sadekbaroudi/vulpes-minora/case/mx/vmin-mx-cirque-bottom-left.stl

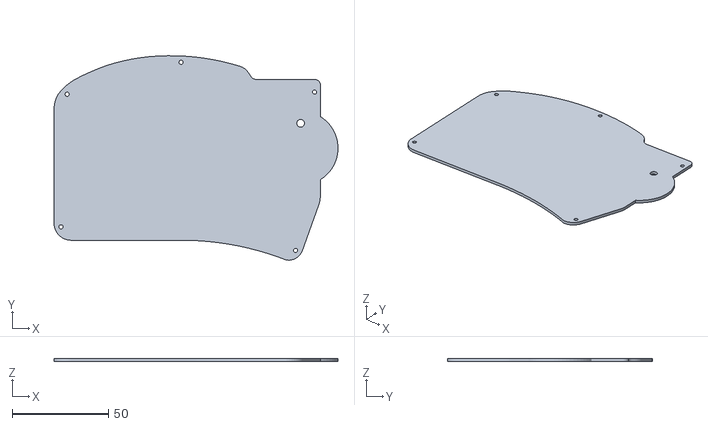
[picture p21: CAD file, 2024-04-24]
case/mx/vmin-mx-cirque-bottom-left.stl
147.2 x 106.0 x 1.60
