sadekbaroudi/vulpes-minora/case/mx/vmin-mx-wireless-cirque-bottom-right.stl

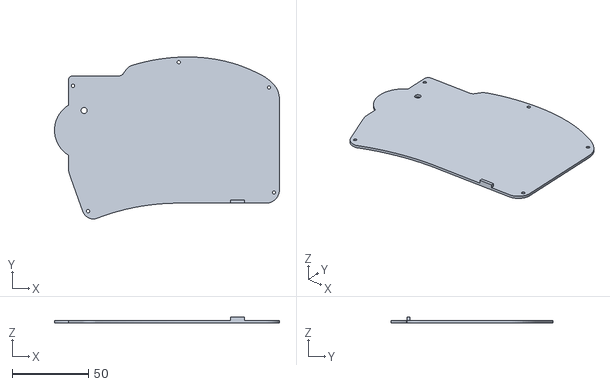
[picture p22: CAD file, 2024-04-24]
case/mx/vmin-mx-wireless-cirque-bottom-right.stl
147.2 x 106.0 x 3.60
