sadekbaroudi/vulpes-minora/case/mx/vmin-vik-peacock-cover.stl

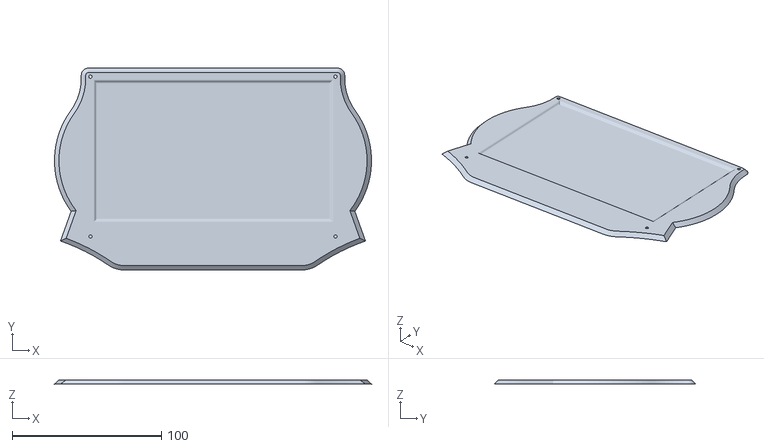
[picture p23: CAD file, 2024-02-21]
case/mx/vmin-vik-peacock-cover.stl
212.2 x 135.2 x 3.00
