sadekbaroudi/vulpes-minora/case/mx/vmin-mx-vik-peacock.stl

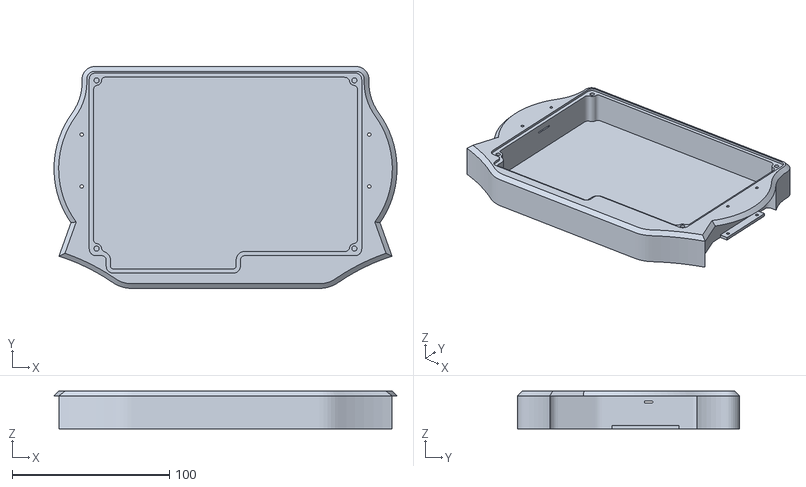
[picture p24: CAD file, 2024-02-19]
case/mx/vmin-mx-vik-peacock.stl
218.2 x 141.2 x 24.0
