sadekbaroudi/vulpes-minora/case/mx/vmin-xivik-mx-vik-waveshare-left.stl

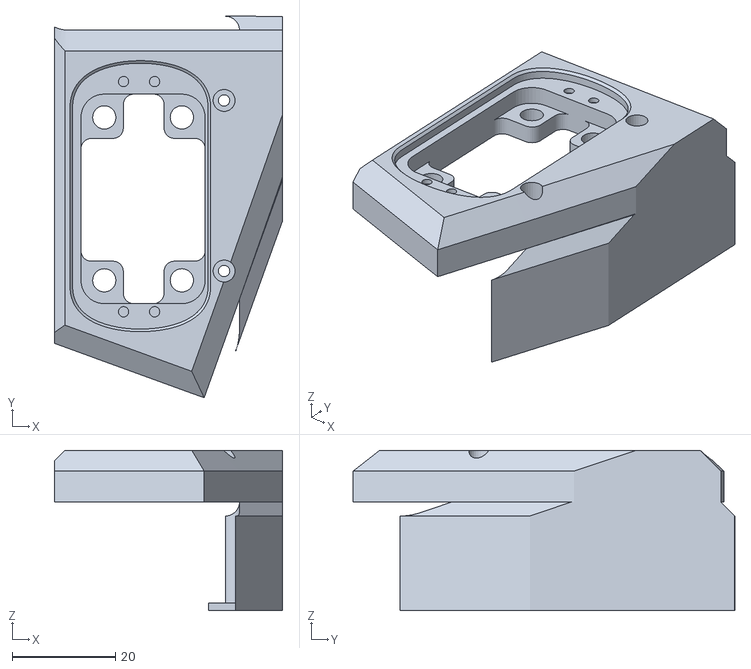
[picture p25: CAD file, 2023-12-03]
case/mx/vmin-xivik-mx-vik-waveshare-left.stl
44.1 x 73.8 x 31.0
