sadekbaroudi/vulpes-minora/case/mx/vmin-xivik-mx-body-left.stl

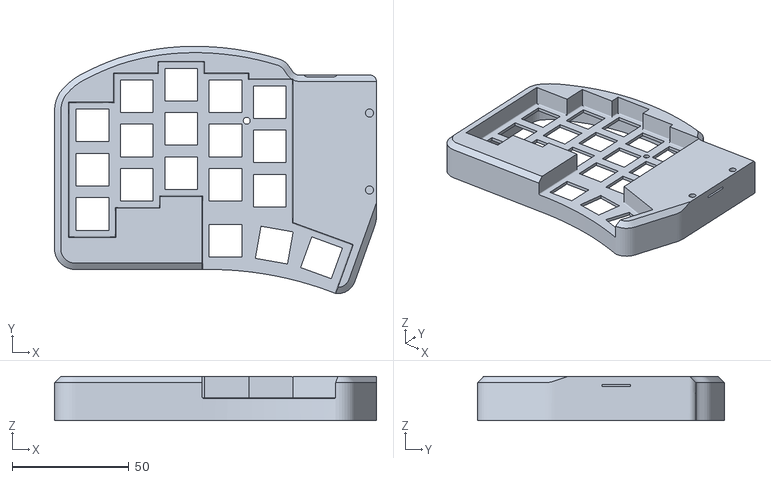
[picture p26: CAD file, 2023-12-01]
case/mx/vmin-xivik-mx-body-left.stl
138.1 x 106.0 x 19.0
