sadekbaroudi/vulpes-minora/case/mx/vmin-pers-cirque-mount-1mm-taller.stl

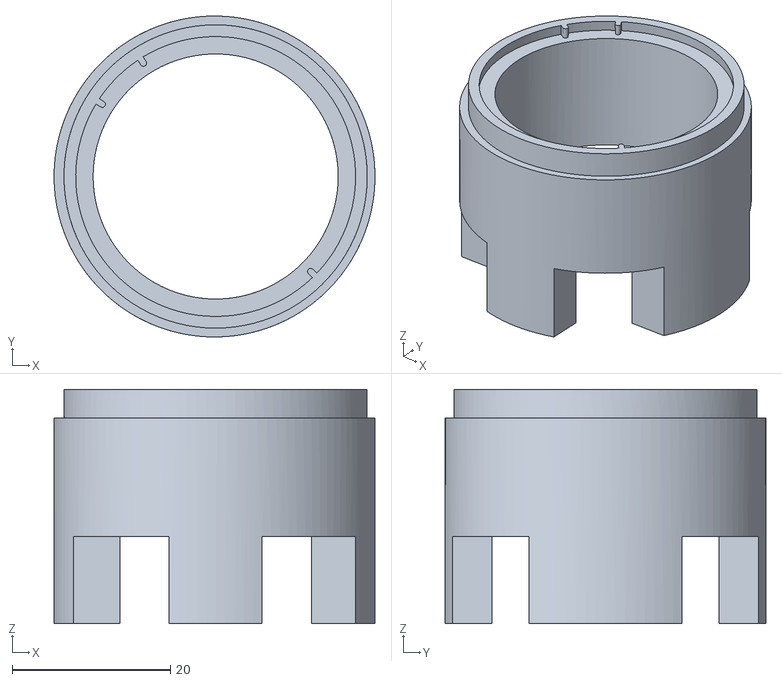
[picture p27: CAD file, 2023-06-04]
case/mx/vmin-pers-cirque-mount-1mm-taller.stl
40.6 x 40.6 x 29.6
