sadekbaroudi/vulpes-minora/case/mx/vmin-pers-cirque-mount.stl

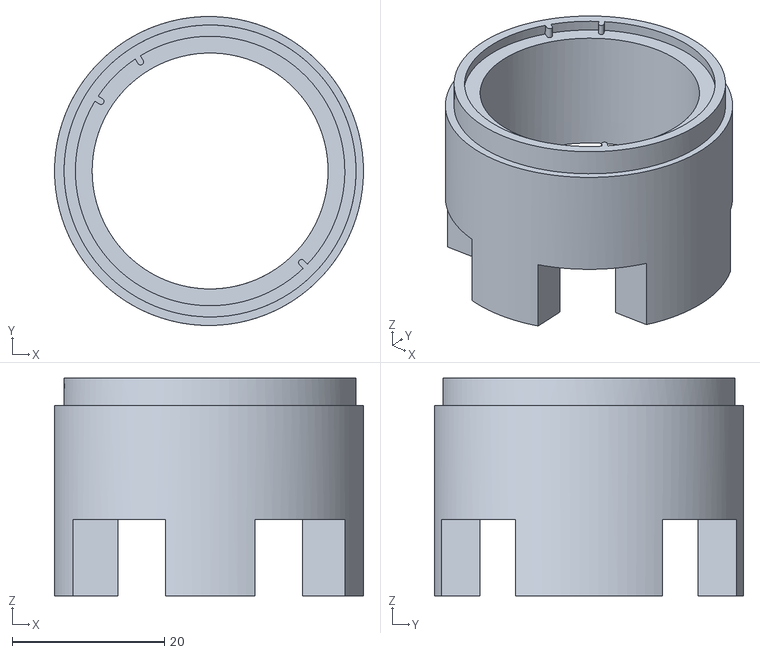
[picture p28: CAD file, 2023-06-04]
case/mx/vmin-pers-cirque-mount.stl
40.6 x 40.6 x 28.6
