sadekbaroudi/vulpes-minora/case/mx/vmin-pers-cirque-mount-scrollwheel.stl

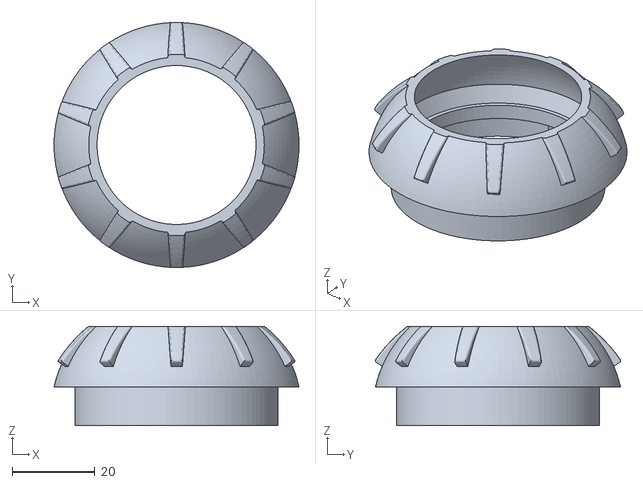
[picture p29: CAD file, 2023-06-04]
case/mx/vmin-pers-cirque-mount-scrollwheel.stl
59.1 x 59.2 x 24.0
