sadekbaroudi/vulpes-minora/case/mx/vmin-mx-ec11-body-left.stl

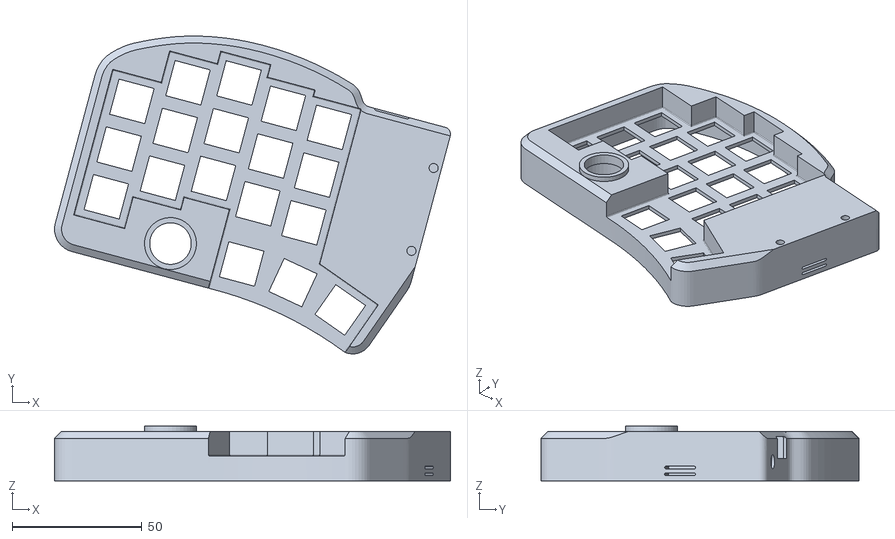
[picture p30: CAD file, 2023-06-03]
case/mx/vmin-mx-ec11-body-left.stl
152.4 x 122.3 x 21.0
