sadekbaroudi/vulpes-minora/case/mx/vmin-pers-cirque-case-module.stl

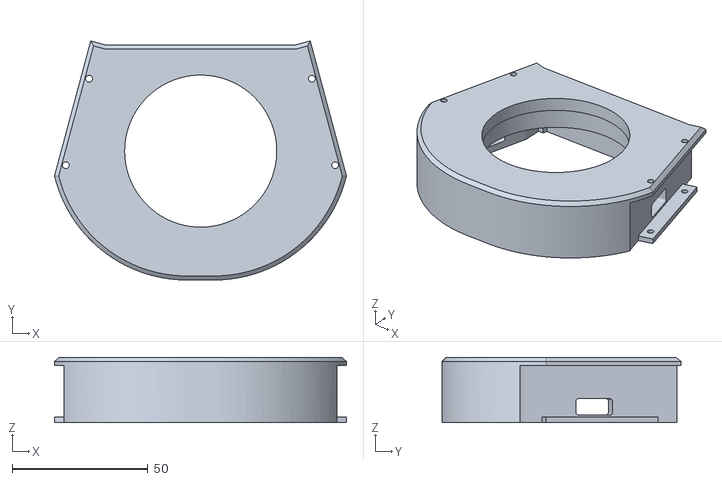
[picture p31: CAD file, 2023-06-03]
case/mx/vmin-pers-cirque-case-module.stl
107.5 x 88.0 x 24.0
